ChaseDurand/Vestax-PDX-2000-Phono-Preamp/spice/Vestax PDX-2000 Phono v1.1.asc

C0: cap; {mc{360e-12,tol}}
C1: cap; {mc{2700e-12,tol}}
C2: cap; {mc{.022e-6,tol}}
C3: cap; {mc{110e-12,tol}}
C4: cap; {mc{6800e-12,tol}}
C5: cap; {mc{2.2e-9,tol}}
C6: cap; {mc{.022e-6,tol}}
C7: cap; {mc{2700e-12,tol}}
C8: cap; {mc{6800e-12,tol}}
C9: cap; {mc{110e-12,tol}}
C10: cap; {mc{2.2e-9,tol}}
C11: cap; {mc{360e-12,tol}}
E_cart: e; laplace ((75e-6*s+1)*(3180e-6*s+1))/((318e-6*s+1))
R0: res; {mc{47k,tol}}
R1: res; {mc{100,tol}}
R2: res; {mc{82k,tol}}
R3: res; {mc{47k,tol}}
R4: res; {mc{4.7k,tol}}
R5: res; {mc{6.2k,tol}}
R6: res; {mc{240,tol}}
R7: res; {mc{100,tol}}
R8: res; {mc{82k,tol}}
R9: res; {mc{4.7k,tol}}
R10: res; {mc{47k,tol}}
R11: res; {mc{47k,tol}}
R12: res; {mc{6.2k,tol}}
R13: res; {mc{240,tol}}
R_load1: res; 10k
R_load: res; 10k
U1: opamp2; LM4562
U2: opamp2; LM4562
V_cart: voltage; ""; AC 0.7071m
V_cart_inv: voltage; ""; AC 0.7071m
Vn: voltage; -12
Vp: voltage; 12
Named nets: 0, OUT_INV, IN_INV, +12V, -12V, OUT, IN
.inc LM4562Fixed.LIB
.ac dec 50 20 20k
.step param X 0 50 1 ; Monte Carlo runs
.param tol=.01 ; +/- 1% component tolerance
.inc LM4562Fixed.LIB
